stasiselectronics/MicroBBPS/Hardware Files/Images/IMG_8848.jpg

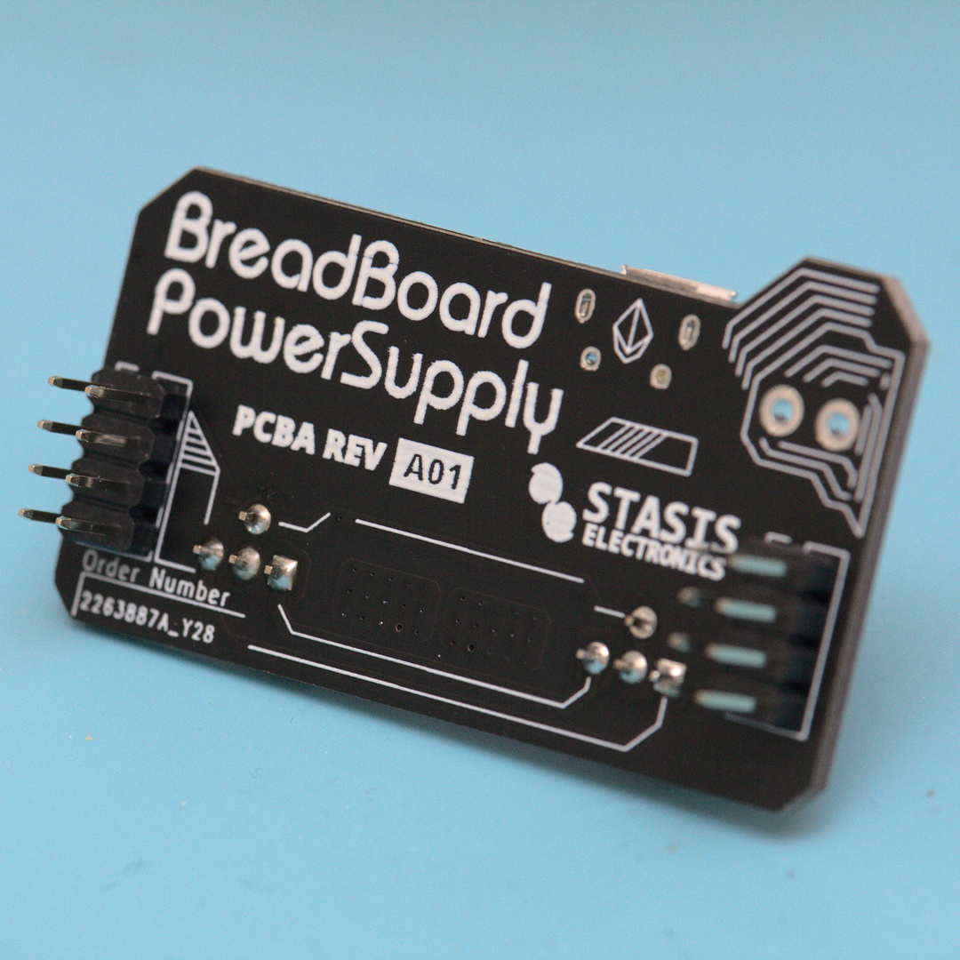
Hardware Files/Images/IMG_8848.jpg
