stasiselectronics/MicroBBPS/Hardware Files/Images/IMG_8854.jpg

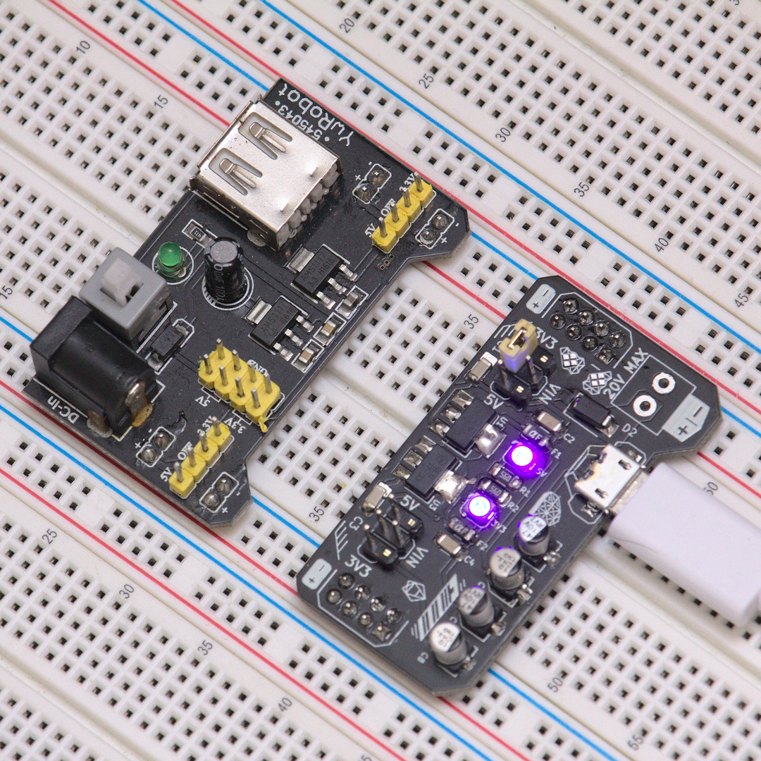
Hardware Files/Images/IMG_8854.jpg
