stasiselectronics/MicroBBPS/Hardware Files/Images/IMG_8864.jpg

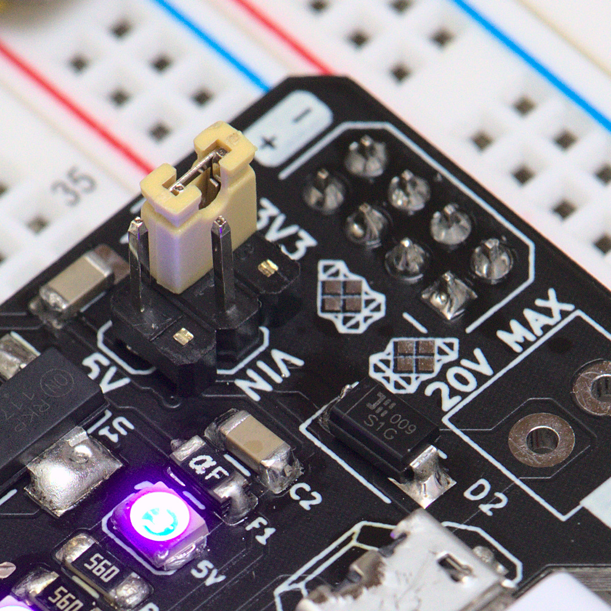
Hardware Files/Images/IMG_8864.jpg
